vasanza/TSC-Lab/Practice11/Practice11_Byte2017/Practice11_Byte.JPG

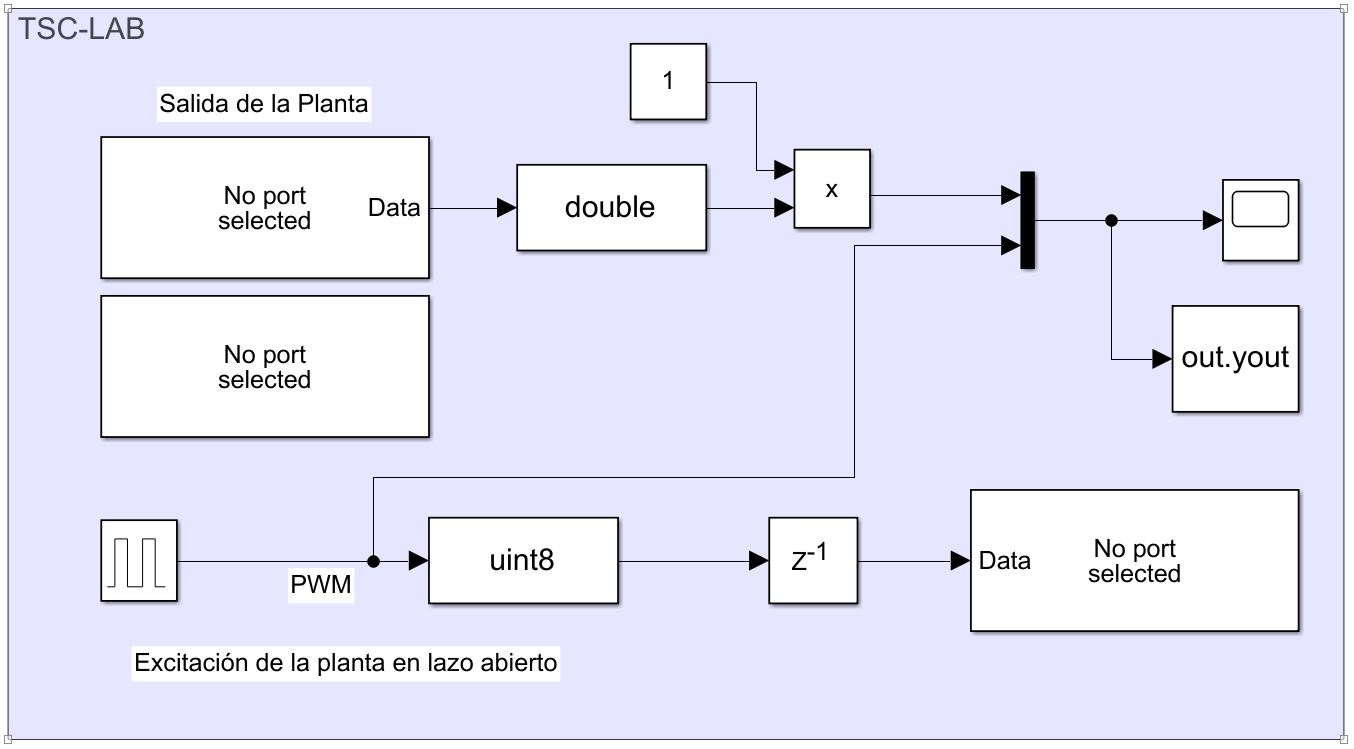
Practice11/Practice11_Byte2017/Practice11_Byte.JPG
