vasanza/TSC-Lab/Practice19_20/Practica19_20/String.JPG

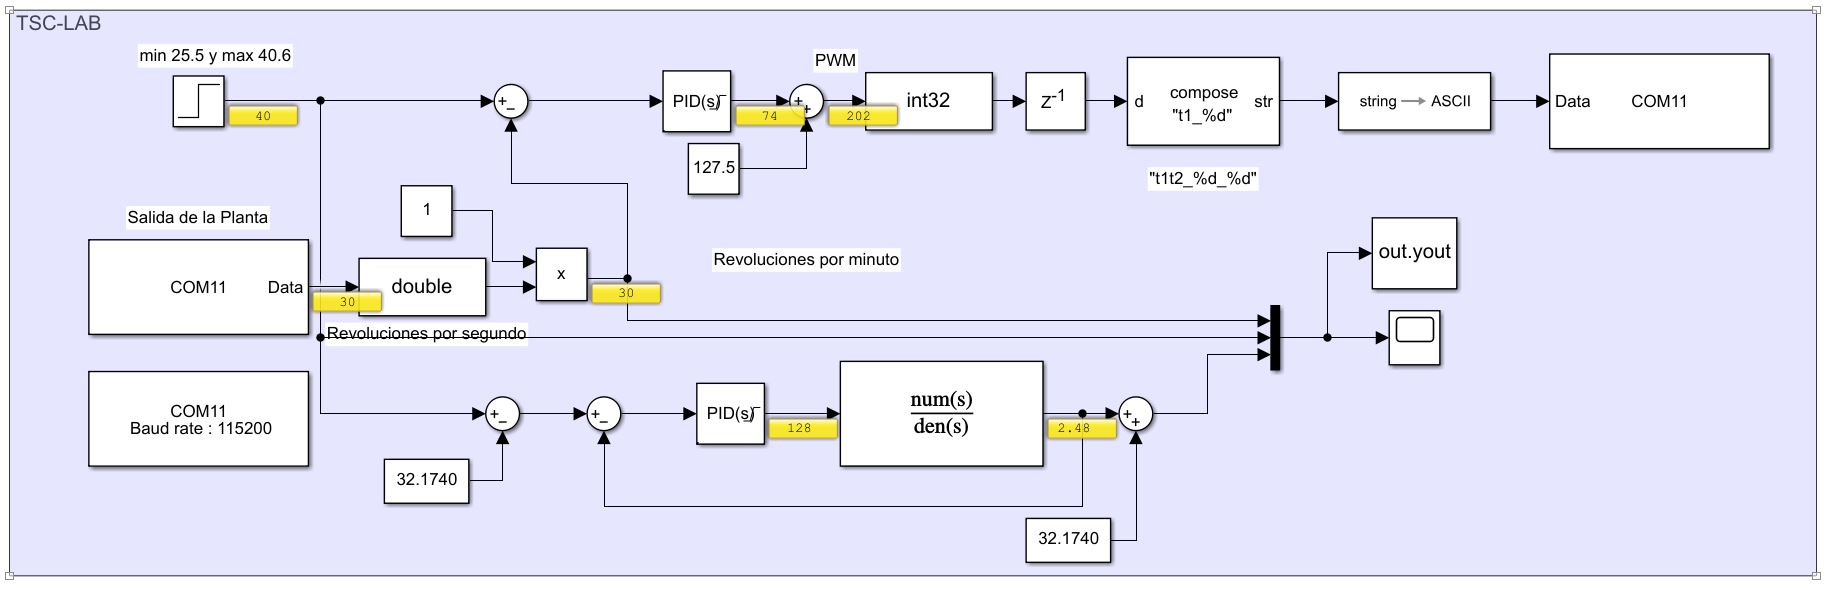
Practice19_20/Practica19_20/String.JPG
