vasanza/TSC-Lab/Practice19_20/Practica19_20_Byte2017/Byte.JPG

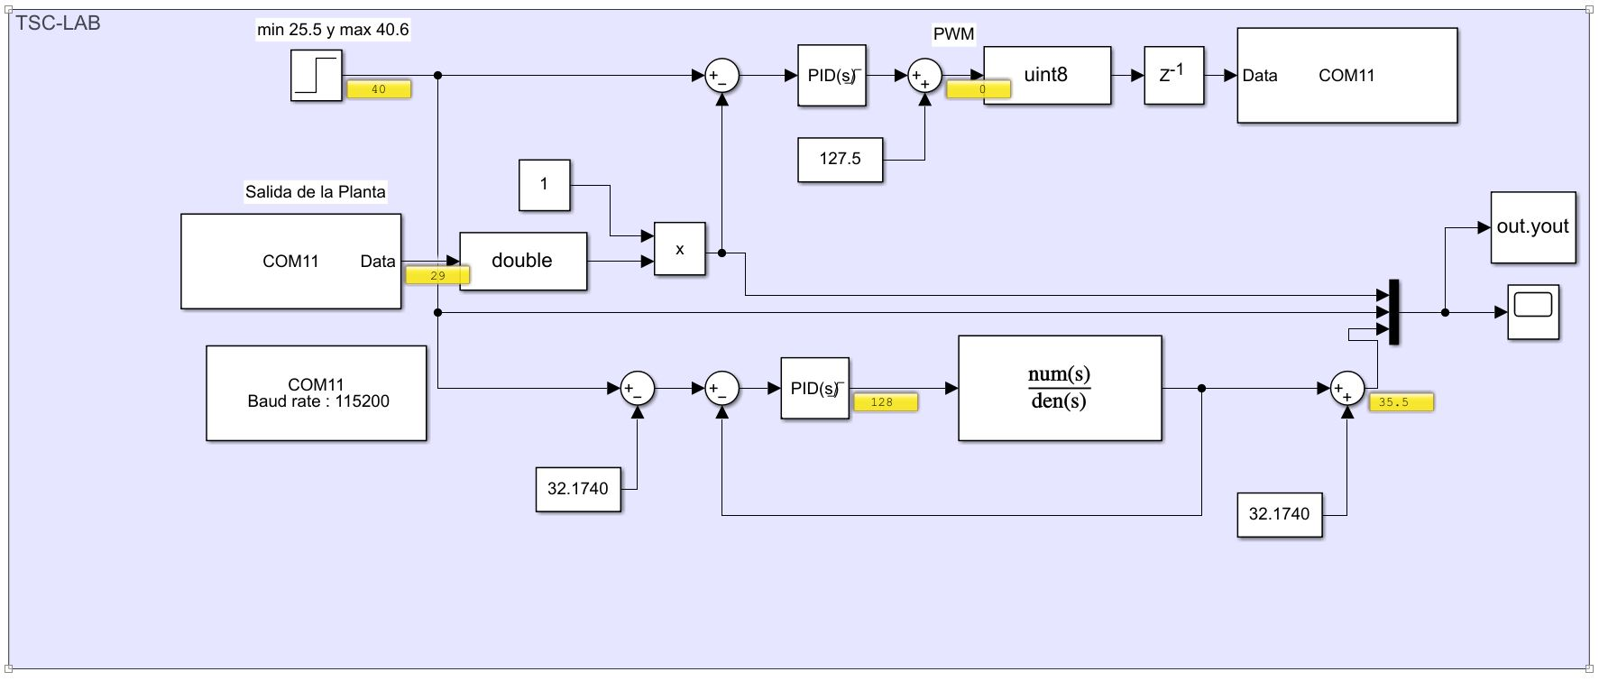
Practice19_20/Practica19_20_Byte2017/Byte.JPG
