vasanza/TSC-Lab/TSC-Lab/PCB1.jpeg

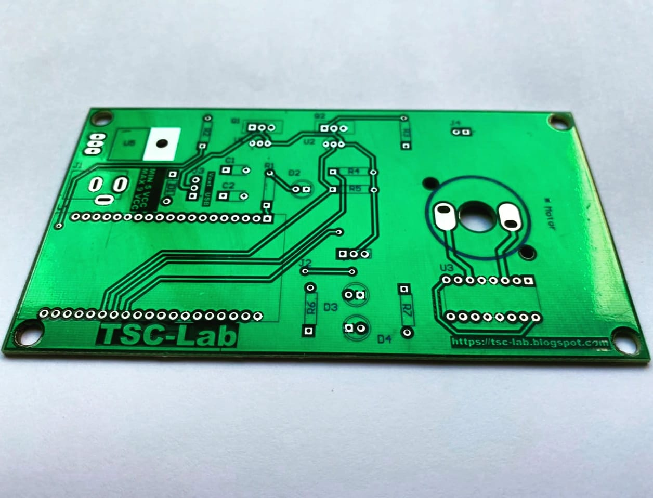
TSC-Lab/PCB1.jpeg
