vasanza/TSC-Lab/Practice13_14/TestOpenLoop.JPG

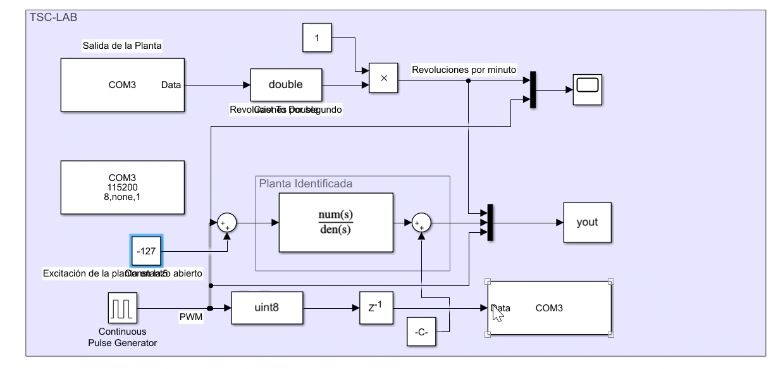
Practice13_14/TestOpenLoop.JPG
