vasanza/TSC-Lab/Practice35/Practice35.ino

//temperaure
#include <OneWire.h>
#include <DallasTemperature.h>

//GPIO pin 0 is set as OneWire bus
OneWire ourWire1(0);
//GPIO pin 4 is set as OneWire bus
OneWire ourWire2(4);

//A variable or object is declared for our sensor 1
DallasTemperature sensors1(&ourWire1);
//A variable or object is declared for our sensor 2
DallasTemperature sensors2(&ourWire2);


//deep sleep

#define uS_TO_S_FACTOR 1000000  /* Conversion factor for micro seconds to seconds */
#define TIME_TO_SLEEP  5        /* Time ESP32 will go to sleep (in seconds) */

RTC_DATA_ATTR int bootCount = 0;

/*
  Method to print the reason by which ESP32
  has been awaken from sleep
*/
void print_wakeup_reason() {
  esp_sleep_wakeup_cause_t wakeup_reason;

  wakeup_reason = esp_sleep_get_wakeup_cause();

  switch (wakeup_reason)
  {
    case ESP_SLEEP_WAKEUP_EXT0 : Serial.println("Wakeup caused by external signal using RTC_IO"); break;
    case ESP_SLEEP_WAKEUP_EXT1 : Serial.println("Wakeup caused by external signal using RTC_CNTL"); break;
    case ESP_SLEEP_WAKEUP_TIMER : Serial.println("Wakeup caused by timer"); break;
    case ESP_SLEEP_WAKEUP_TOUCHPAD : Serial.println("Wakeup caused by touchpad"); break;
    case ESP_SLEEP_WAKEUP_ULP : Serial.println("Wakeup caused by ULP program"); break;
    default : Serial.printf("Wakeup was not caused by deep sleep: %d\n", wakeup_reason); break;
  }
}

void setup() {
  Serial.begin(115200);
  delay(1000); //Take some time to open up the Serial Monitor

  sensors1.begin();   //Sensor 1 starts
  sensors2.begin();   //Sensor 2 starts

  //Increment boot number and print it every reboot
  ++bootCount;
  Serial.println("Boot number: " + String(bootCount));

  //Print the wakeup reason for ESP32
  print_wakeup_reason();

  /*
    First we configure the wake up source
    We set our ESP32 to wake up every 5 seconds
  */
  esp_sleep_enable_timer_wakeup(TIME_TO_SLEEP * uS_TO_S_FACTOR);
  Serial.println("Setup ESP32 to sleep for every " + String(TIME_TO_SLEEP) +
                 " Seconds");

  //function for reading temperatures
  readTemperature();


  Serial.println("Going to sleep now");
  delay(1000);
  Serial.flush();
  esp_deep_sleep_start();
  Serial.println("This will never be printed");
}

void loop() {
  //This is not going to be called
}

void readTemperature() {
  //The command is sent to read the temperature
  sensors1.requestTemperatures();
  //Obtain the temperature in ºC of sensor 1
  float temp1 = sensors1.getTempCByIndex(0);

  //The command is sent to read the temperature
  sensors2.requestTemperatures();
  //Obtain the temperature in ºC of sensor 2
  float temp2 = sensors2.getTempCByIndex(0);

  //print to display the temperature change
  Serial.println();
  Serial.println("Temperatures:");
  Serial.print(temp1);
  Serial.print(",");
  Serial.println(temp2);
}
